MakeYourPet/hexapod/Illustrations/top.png

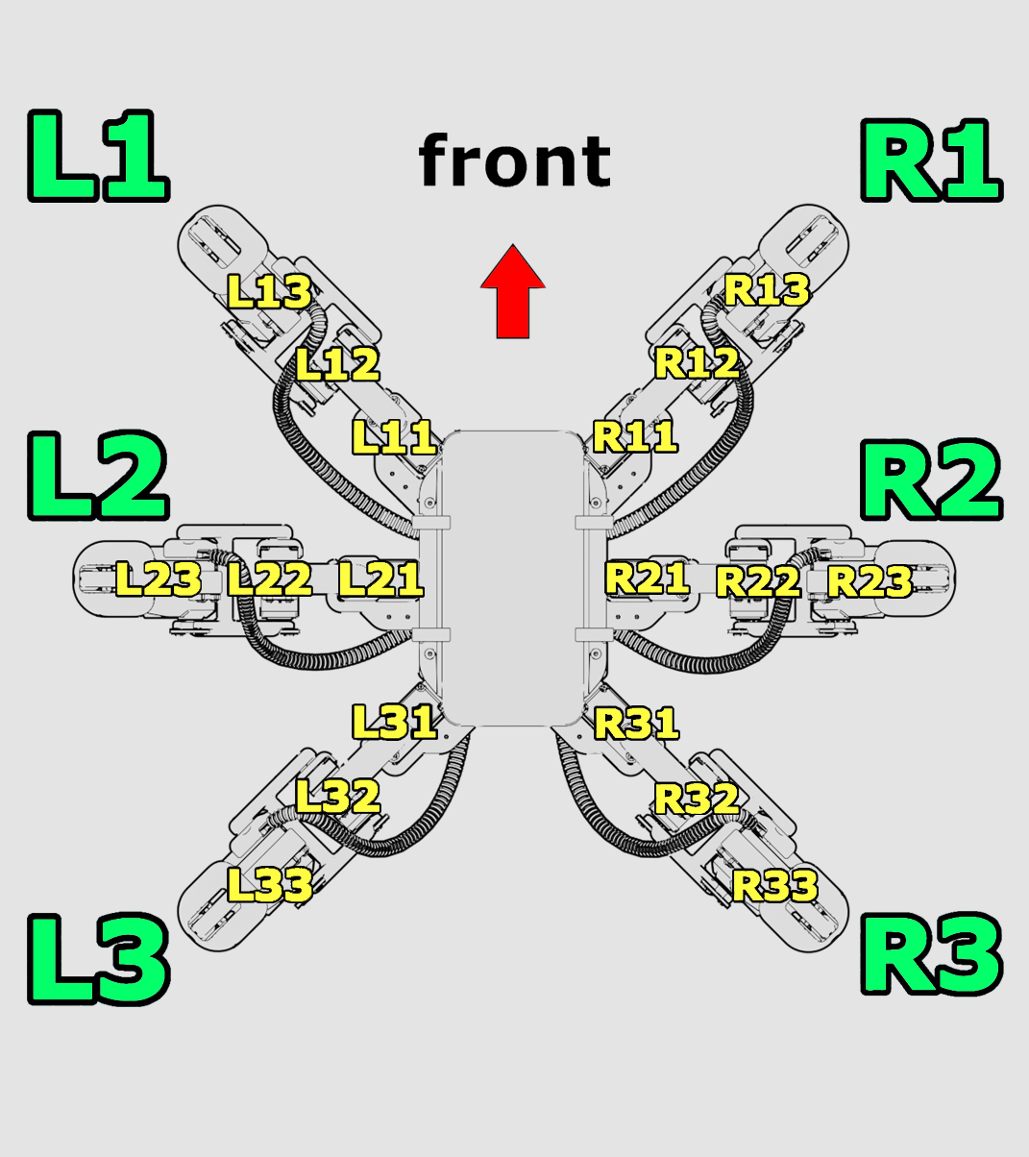
Illustrations/top.png
