MakeYourPet/hexapod/STL/right-femur.stl

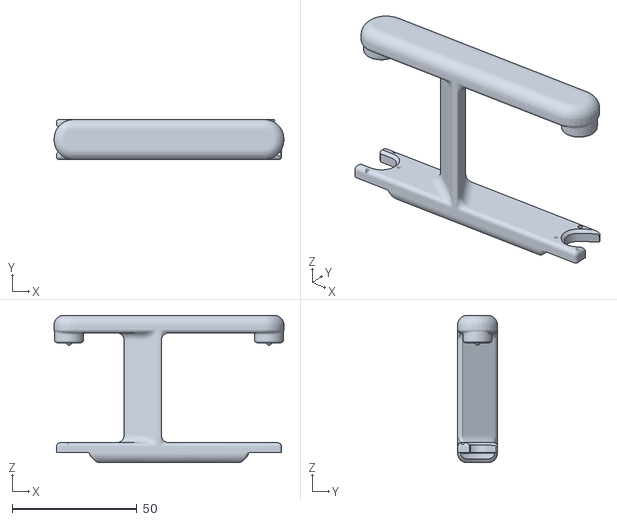
[picture p30: CAD file, 2022-10-04]
STL/right-femur.stl
92.0 x 16.0 x 59.0
