MakeYourPet/hexapod/Chipo/rod.stl

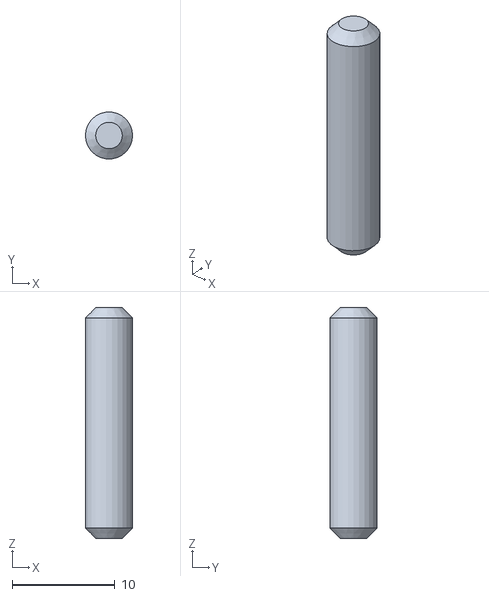
[picture p31: CAD file, 2023-04-09]
Chipo/rod.stl
4.60 x 4.57 x 22.5
