MakeYourPet/hexapod/STL/phone-bar2.stl

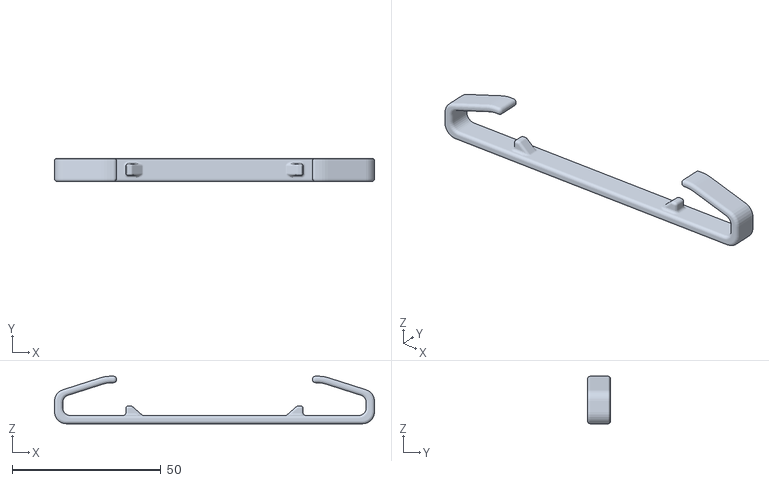
[picture p32: CAD file, 2022-10-04]
STL/phone-bar2.stl
107.6 x 7.80 x 16.0
