MakeYourPet/hexapod/Chipo/coxa-996.stl

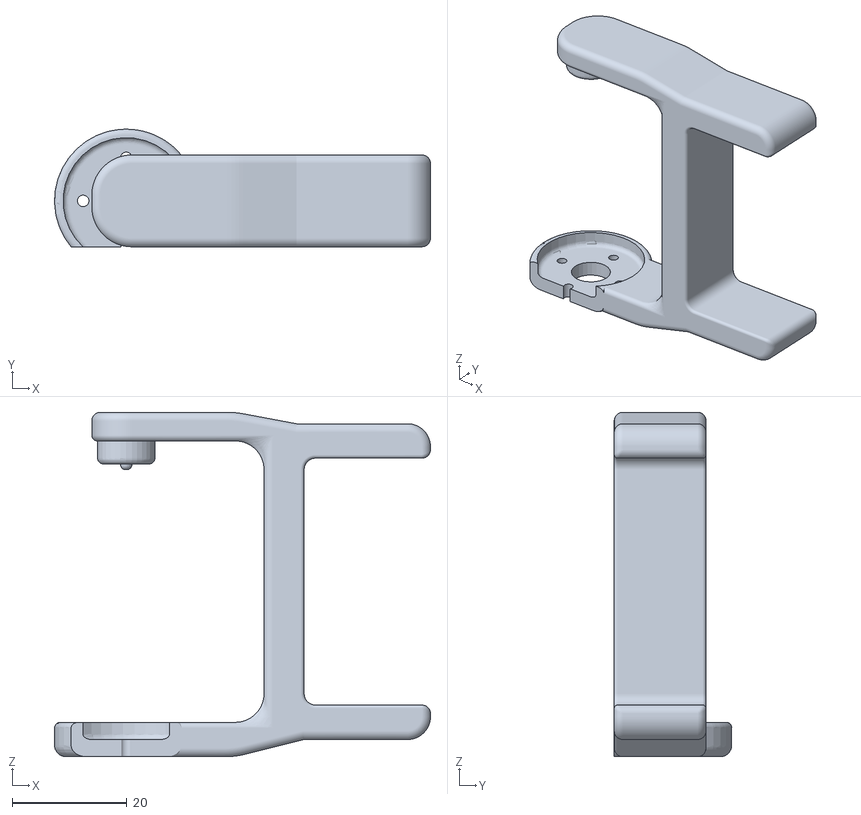
[picture p33: CAD file, 2023-04-09]
Chipo/coxa-996.stl
65.5 x 20.5 x 60.0
