MakeYourPet/hexapod/STEP/limiter.step

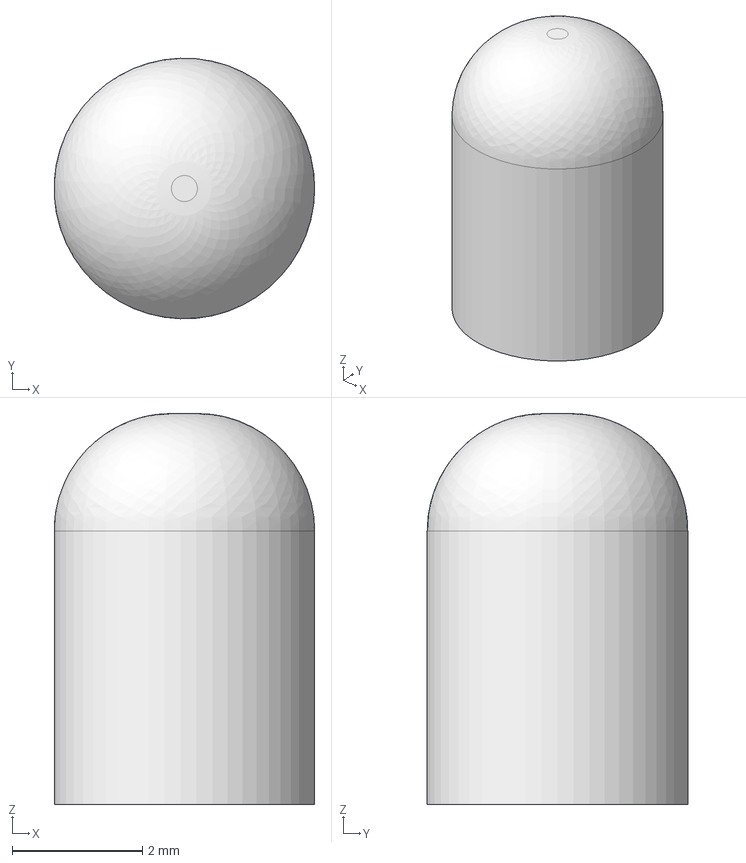
[picture p34: CAD file, 2022-11-02]
STEP/limiter.step
4.00 x 4.00 x 6.00 mm
