MakeYourPet/hexapod/Chipo/ring.stl

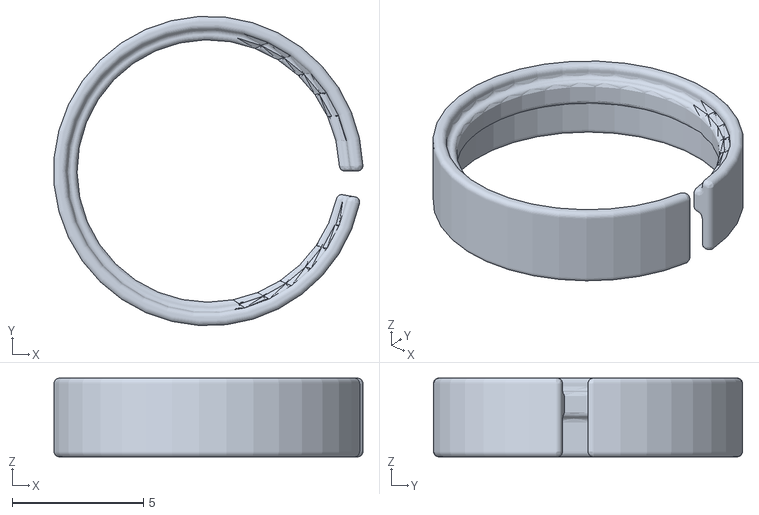
[picture p35: CAD file, 2023-04-09]
Chipo/ring.stl
11.8 x 11.8 x 3.00
