MakeYourPet/hexapod/STL/servo-back-hole2.stl

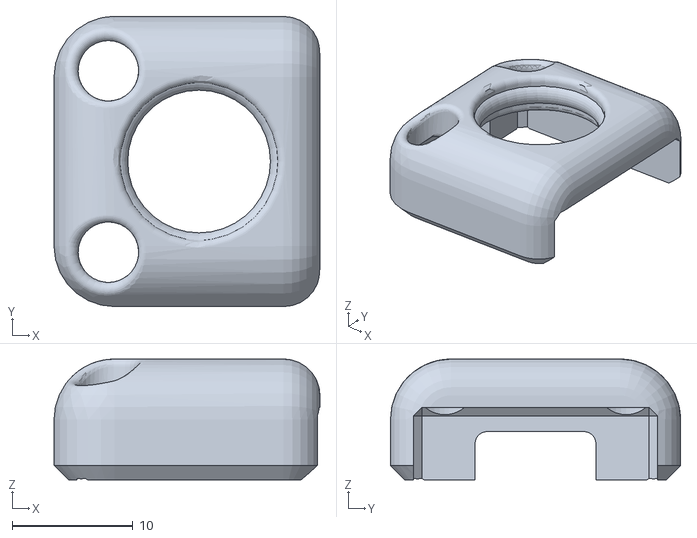
[picture p36: CAD file, 2022-10-04]
STL/servo-back-hole2.stl
22.0 x 24.0 x 10.0
