MakeYourPet/hexapod/Chipo/femur-996.stl

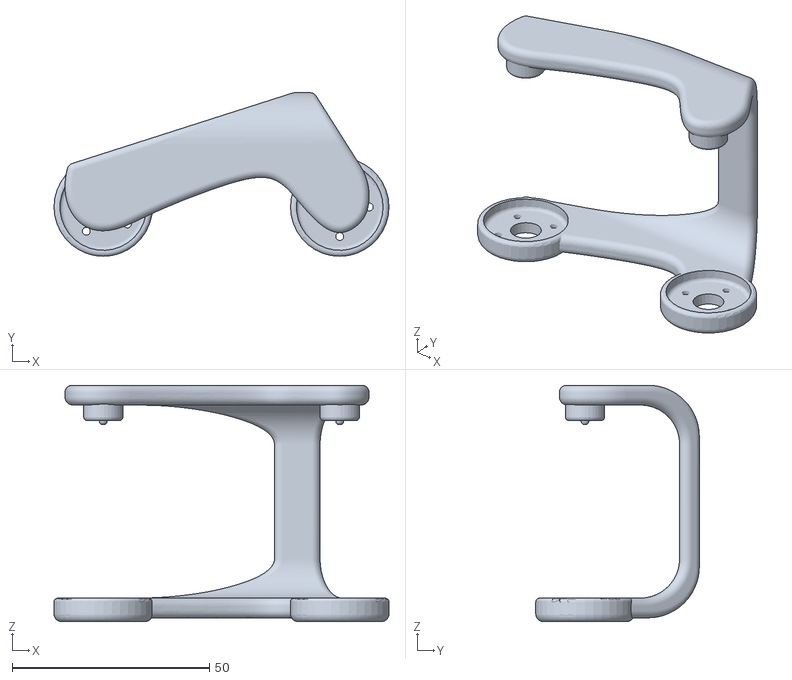
[picture p37: CAD file, 2023-04-09]
Chipo/femur-996.stl
85.0 x 41.5 x 60.0
