MakeYourPet/hexapod/STEP/micro-switch-holder.step

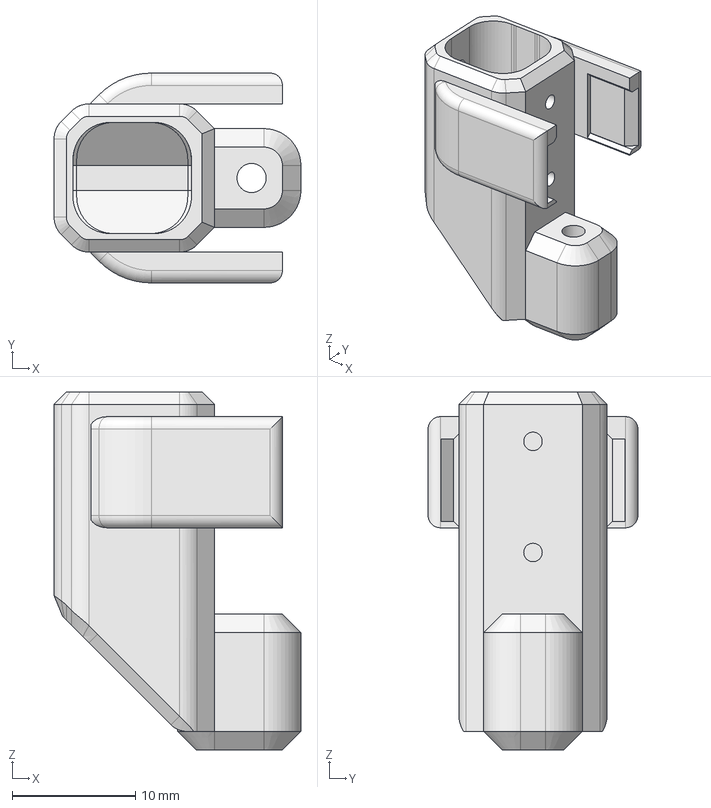
[picture p38: CAD file, 2022-11-02]
STEP/micro-switch-holder.step
20.0 x 17.0 x 29.0 mm
