MakeYourPet/hexapod/STL/right-coxa.stl

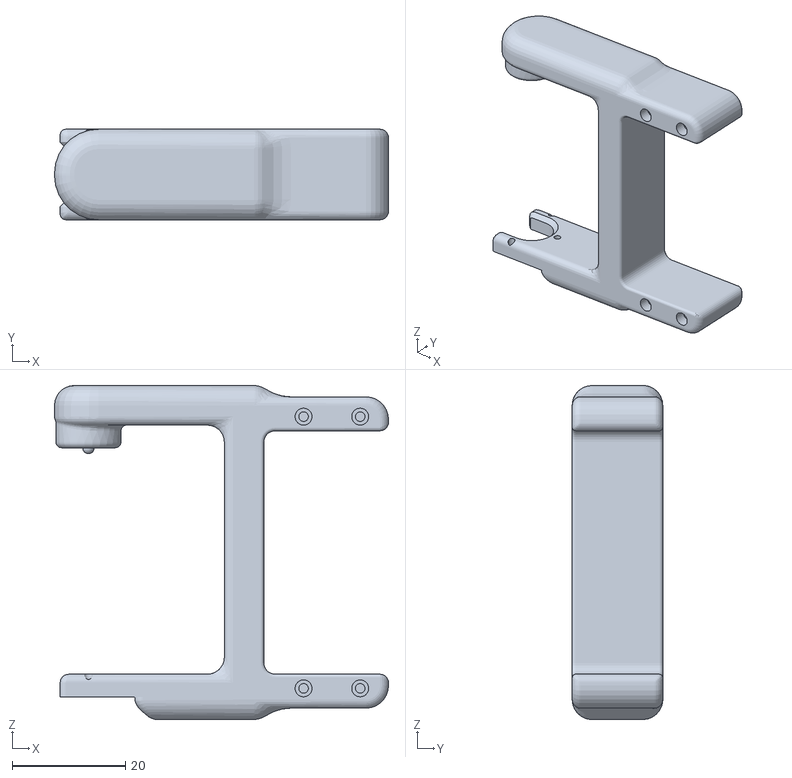
[picture p39: CAD file, 2022-10-04]
STL/right-coxa.stl
59.0 x 16.0 x 59.0
