MakeYourPet/hexapod/Chipo/limitter.stl

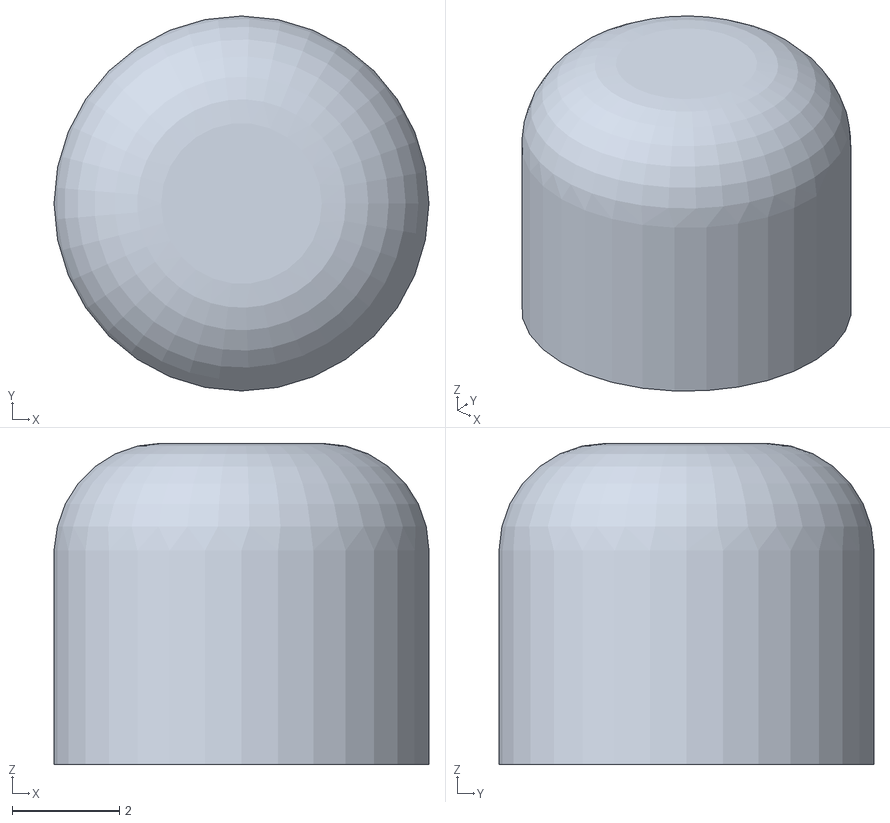
[picture p40: CAD file, 2023-04-09]
Chipo/limitter.stl
7.00 x 7.00 x 6.00
