MakeYourPet/hexapod/STEP/frame.step

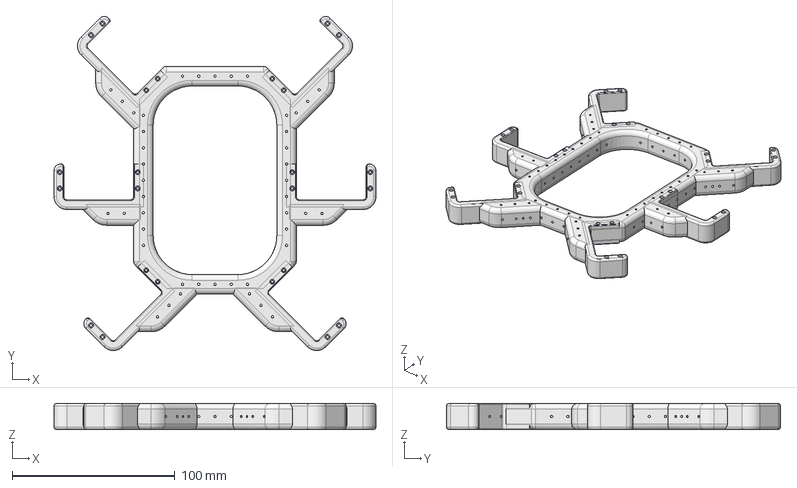
[picture p41: CAD file, 2022-11-02]
STEP/frame.step
198.0 x 205.4 x 16.0 mm
