MakeYourPet/hexapod/STL/right-coxa2.stl

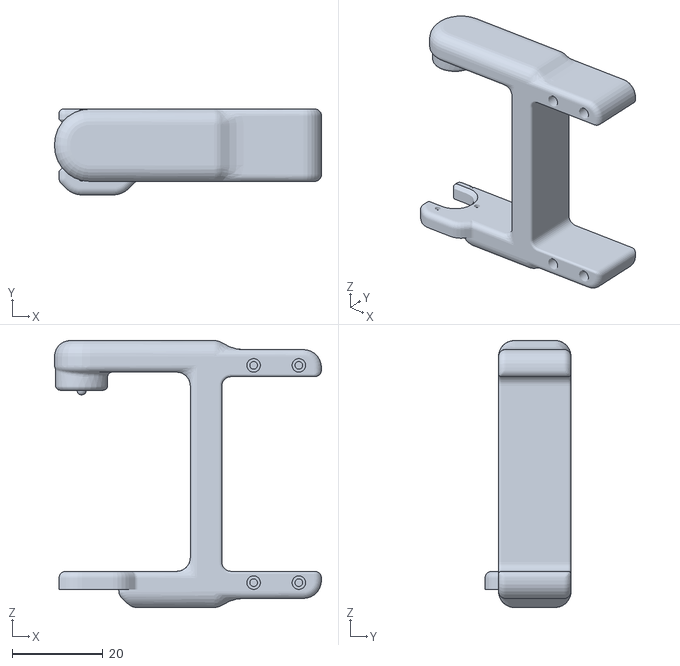
[picture p42: CAD file, 2022-10-04]
STL/right-coxa2.stl
59.0 x 19.0 x 59.0
