MakeYourPet/hexapod/STEP/tibia.step

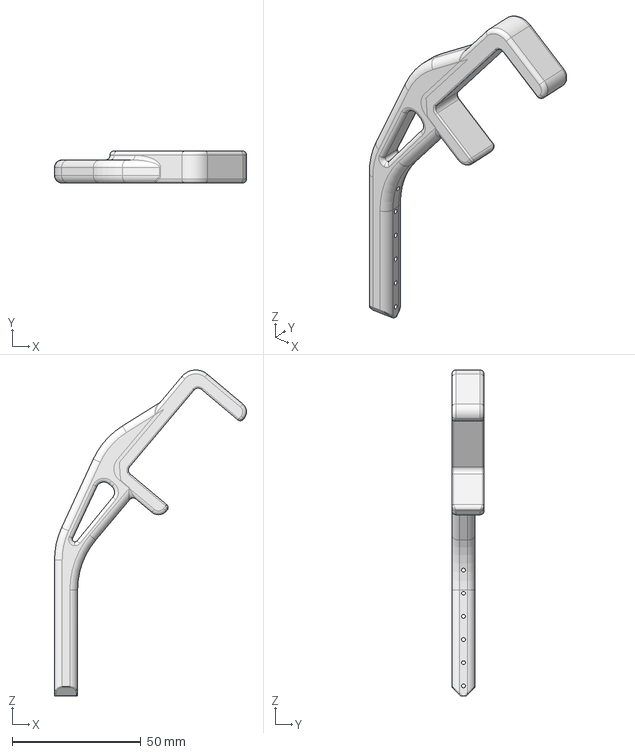
[picture p43: CAD file, 2022-11-02]
STEP/tibia.step
74.6 x 12.5 x 126.7 mm
