MakeYourPet/hexapod/STL/shield.stl

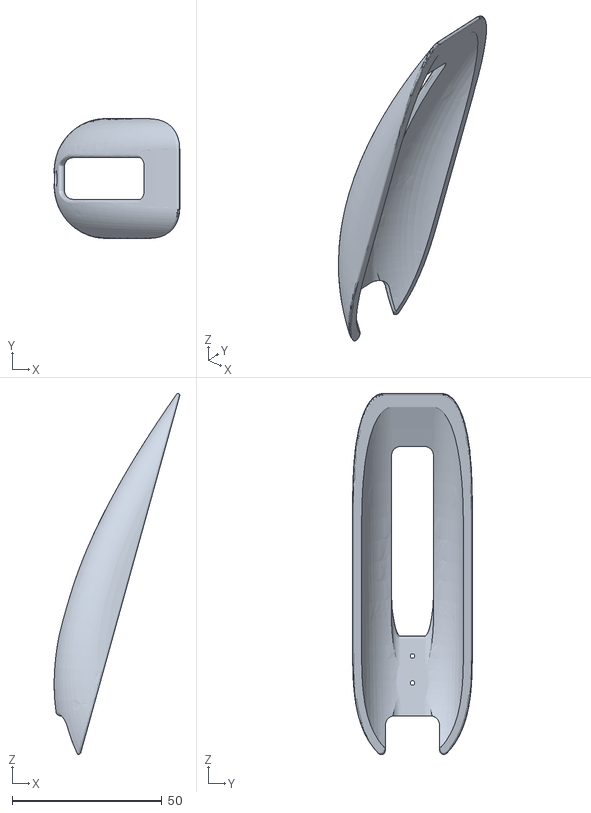
[picture p44: CAD file, 2022-10-04]
STL/shield.stl
42.0 x 40.0 x 120.6
