MakeYourPet/hexapod/STEP/tip.step

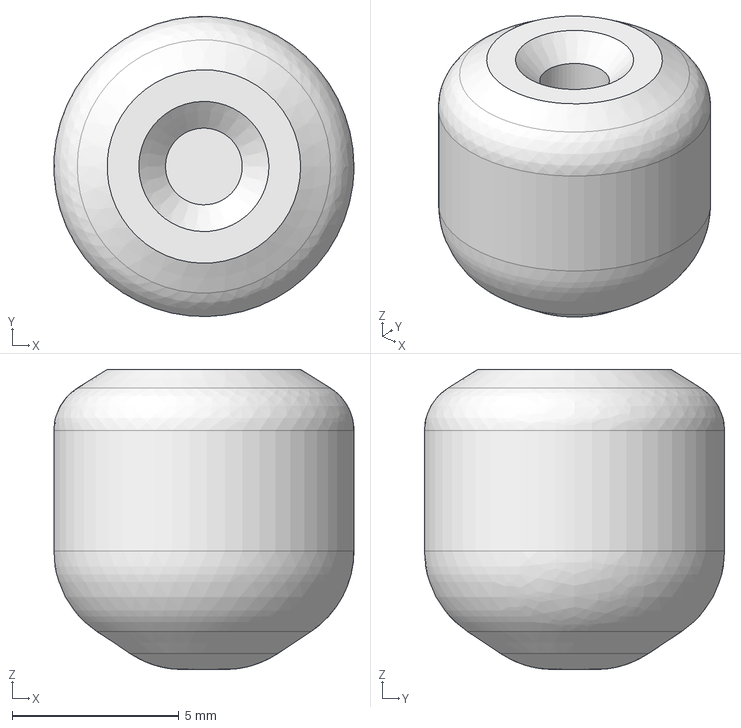
[picture p45: CAD file, 2022-11-02]
STEP/tip.step
8.99 x 9.00 x 9.00 mm
