MakeYourPet/hexapod/STL/battery-bar.stl

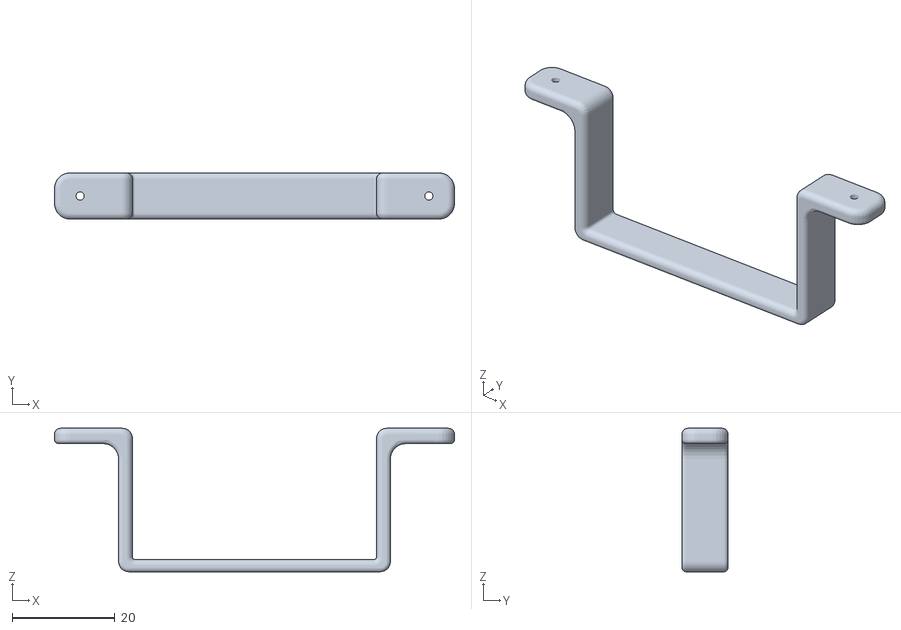
[picture p46: CAD file, 2022-10-04]
STL/battery-bar.stl
78.0 x 9.00 x 28.0
