MakeYourPet/hexapod/STL/top-cover2.stl

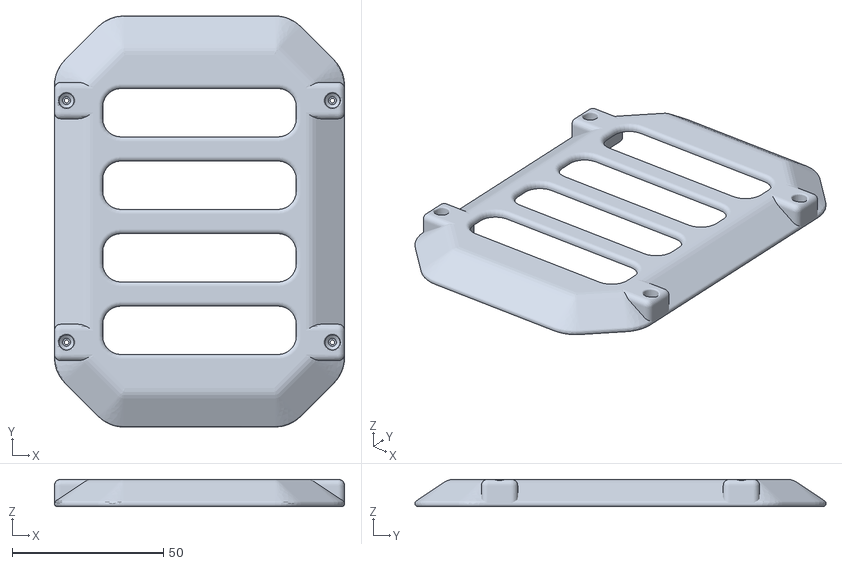
[picture p47: CAD file, 2022-10-04]
STL/top-cover2.stl
96.0 x 136.0 x 9.00
